vascofazza/8bit-cpu/MK1_CPU/code/mk1_computer_uplodader/mk1_computer_uplodader.ino

#define MI 10
#define HL 11
#define RI 12
#define EN 13
#define CLK A0
#define RST A1
#define CU_EN A2

void setup() {
  // put your setup code here, to run once:
  Serial.begin(9600);
  //Serial.setTimeout(5000);
  pinMode(MI, OUTPUT);
  pinMode(HL, OUTPUT);
  pinMode(RI, OUTPUT);
  pinMode(EN, OUTPUT);
  pinMode(CLK, INPUT);
  pinMode(RST, INPUT);
  pinMode(CU_EN, OUTPUT);

  DDRD |= B11111100;
  DDRB |= B00000011;
}

void reset()
{
  pinMode(RST, OUTPUT);
  digitalWrite(RST, HIGH);
  delayMicroseconds(10);
  digitalWrite(RST, LOW);
  pinMode(RST, INPUT);
}

void clock()
{
  pinMode(CLK, OUTPUT);
  digitalWrite(CLK, HIGH);
  delayMicroseconds(1);
  digitalWrite(CLK, LOW);
  pinMode(CLK, INPUT);
}

void enableClock()
{
  pinMode(CLK, OUTPUT);
  digitalWrite(CLK, HIGH);
}

void disableClock()
{
  pinMode(CLK, OUTPUT);
  digitalWrite(CLK, LOW);
  pinMode(CLK, INPUT);
}

void disable_cu()
{
  digitalWrite(CU_EN, HIGH);
}

void enable_cu()
{
  digitalWrite(CU_EN, LOW);
}

void enableOutput()
{
  digitalWrite(EN, HIGH);
}

void disableOutput()
{
  digitalWrite(EN, LOW);
}

void setAddress(unsigned int address)
{
  digitalWrite(HL, address > 0xFF);
  putOut(address);
  delayMicroseconds(1);
  enableOutput();
  digitalWrite(MI, HIGH);
  delayMicroseconds(1);
  digitalWrite(MI, LOW);
  delayMicroseconds(1);
  disableOutput();
}

void putOut(byte data)
{
  PORTD = (PORTD & 0x3) | (data << 2);
  PORTB = (PORTB & 0xFC) | (data >> 6 & 0x3);
  delayMicroseconds(1);
}

void writeInstruction(byte instr)
{
  putOut(instr);
  enableOutput();
  delayMicroseconds(1);
  digitalWrite(RI, HIGH);
  delayMicroseconds(1);
  digitalWrite(RI, LOW);
  delayMicroseconds(1);
  disableOutput();
  
}

byte buffer[512];

void loop() {
  if (Serial.available()) {

    int p_size = Serial.readBytes(buffer, sizeof(buffer));
    Serial.write(0);

    reset();
    disable_cu();

    delayMicroseconds(1);
    enableClock();
    delayMicroseconds(1);
    for (int i = 0; i < p_size; i ++)
    {
      setAddress(i);
      delayMicroseconds(1);
      writeInstruction(buffer[i]);
      delayMicroseconds(1);
    }

    disableClock();
    digitalWrite(HL, LOW);
    reset();
    enable_cu();
  }
  disableOutput();

}
